tstrube/Tiwaz/Images/Tiwaz_On.jpg

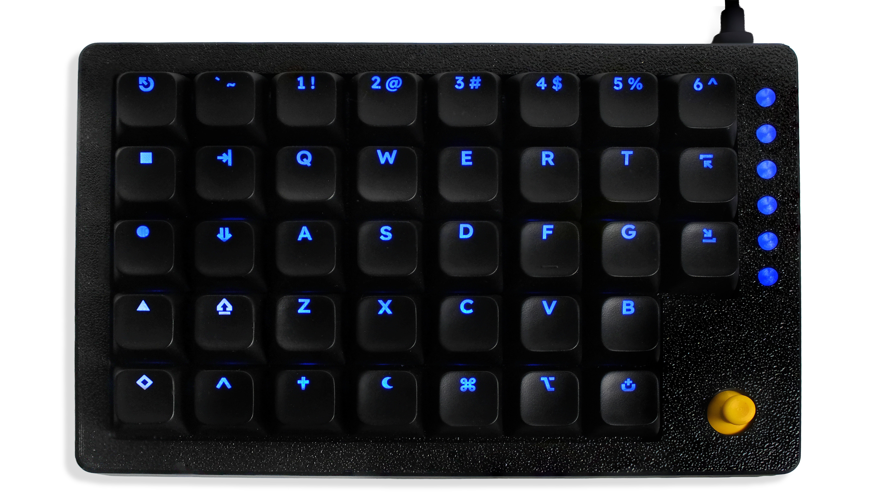
Images/Tiwaz_On.jpg
